kaidegit/ComputerOccupyingMonitor/EmbeddedProject/APP/src/io_config.h

//
// Created by yekai on 2022/3/9.
//

#ifndef CH571PRJ_IO_CONFIG_H
#define CH571PRJ_IO_CONFIG_H

#define MONITOR_CH0_Pin GPIO_Pin_12
#define MONITOR_CH1_Pin GPIO_Pin_13

#define LED_Pin GPIO_Pin_4

#endif //CH571PRJ_IO_CONFIG_H
