kaidegit/ComputerOccupyingMonitor/EmbeddedProject/APP/src/monitor.h

//
// Created by yekai on 2022/3/8.
//

#ifndef CH571PRJ_MONITOR_H
#define CH571PRJ_MONITOR_H

#include "stdint.h"

void Monitor_PWM_Init();

void Monitor_Set_Usage(uint8_t ch, uint16_t usage);

#endif //CH571PRJ_MONITOR_H
